calvin-mcd/the-PETER-keyboard/Images/DSCF4483.JPG

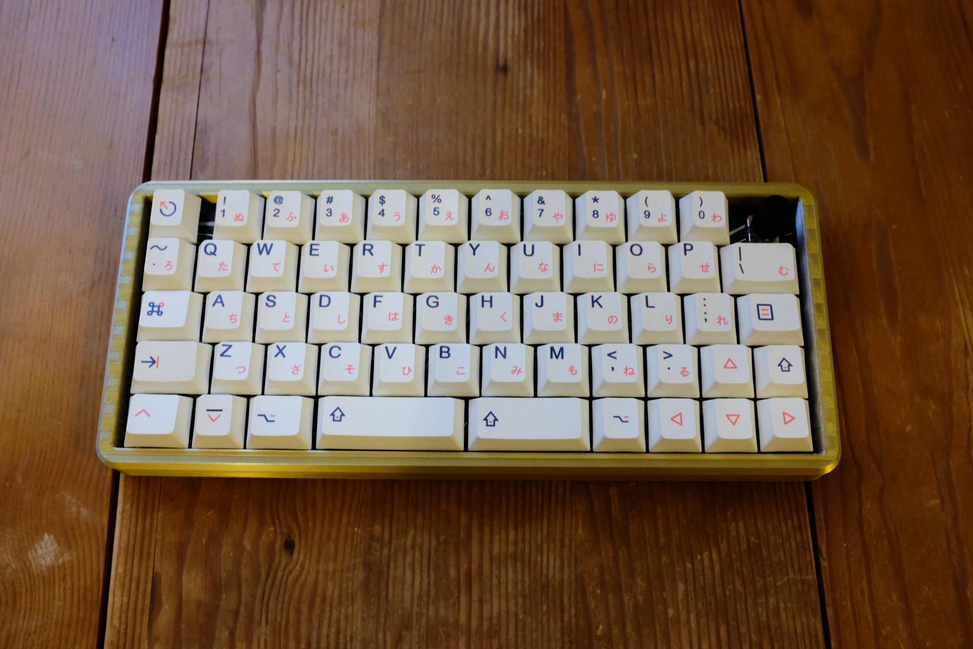
Images/DSCF4483.JPG
