calvin-mcd/the-PETER-keyboard/Images/DSCF4485.JPG

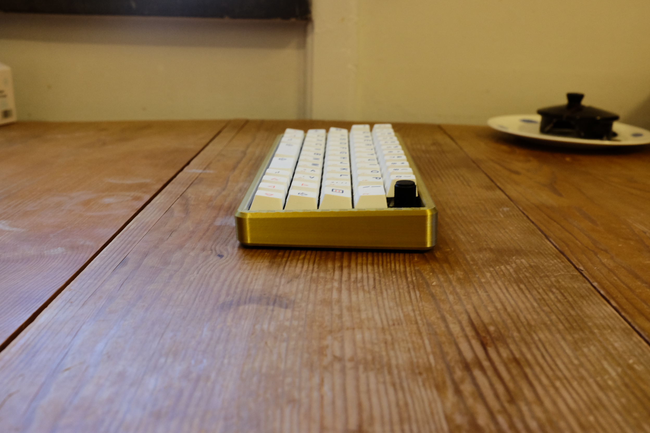
Images/DSCF4485.JPG
