calvin-mcd/the-PETER-keyboard/Images/DSCF4486.JPG

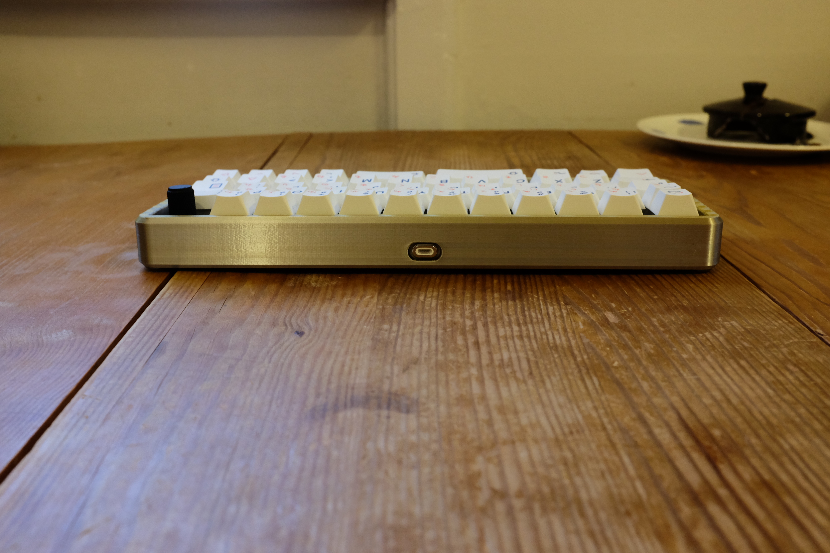
Images/DSCF4486.JPG
