calvin-mcd/the-PETER-keyboard/Images/DSCF4487.JPG

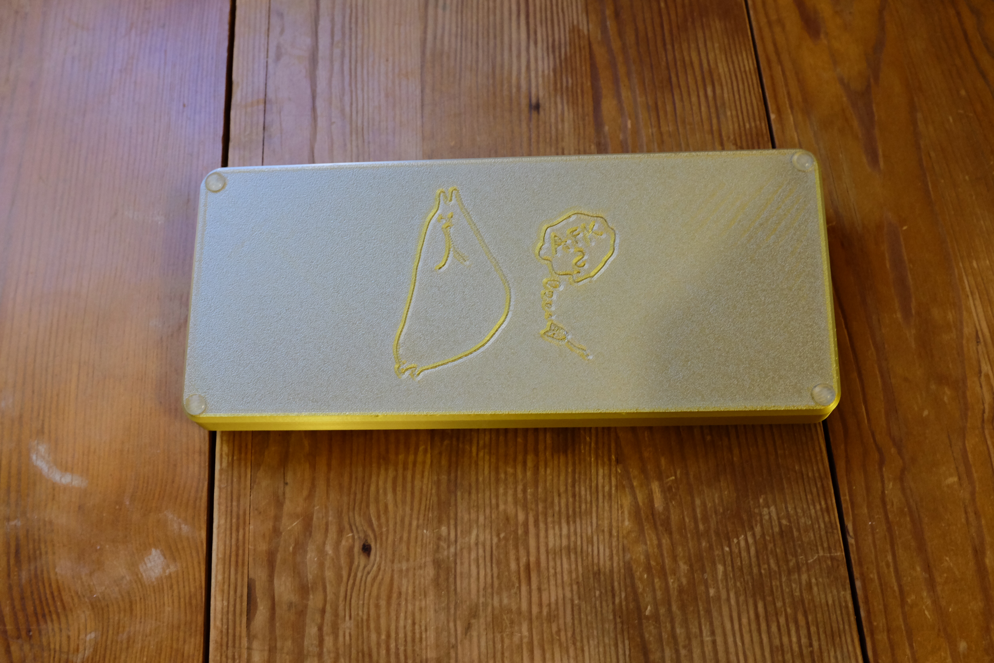
Images/DSCF4487.JPG
