calvin-mcd/the-PETER-keyboard/Images/IMG_2702.jpg

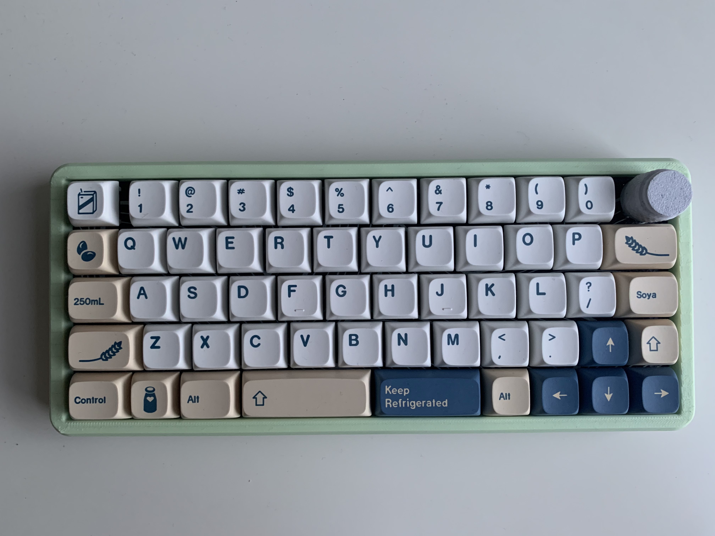
Images/IMG_2702.jpg
